netz39/PowerDelivery_for_Space/3D_models/PowerDelivery_Board.png

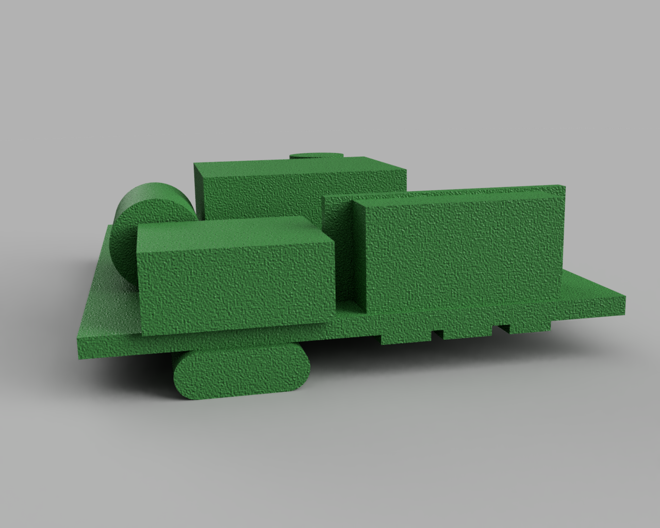
3D_models/PowerDelivery_Board.png
