netz39/PowerDelivery_for_Space/media/animatedView/frame.4.png

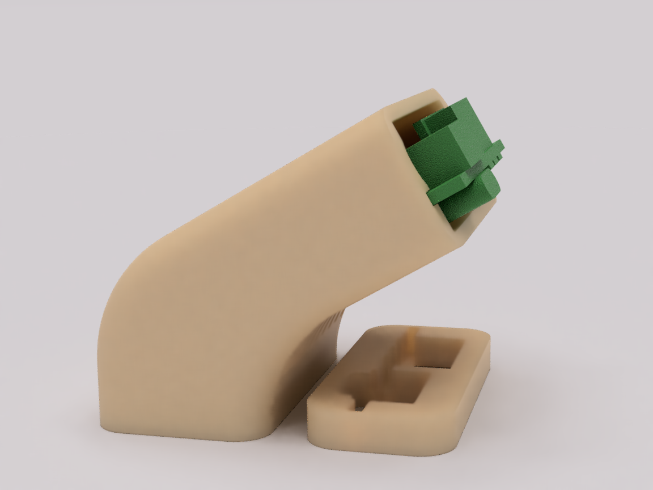
media/animatedView/frame.4.png
