netz39/PowerDelivery_for_Space/media/animatedView/frame.5.png

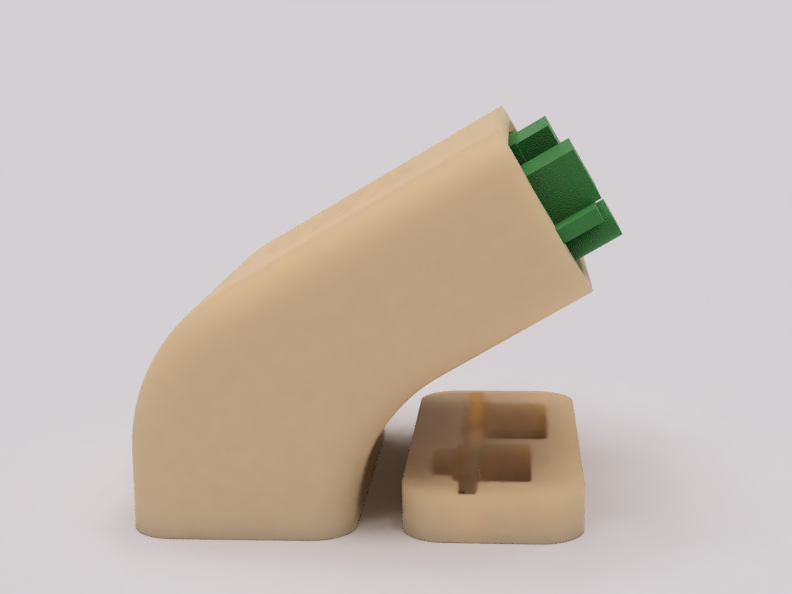
media/animatedView/frame.5.png
