netz39/PowerDelivery_for_Space/media/animatedView/frame.10.png

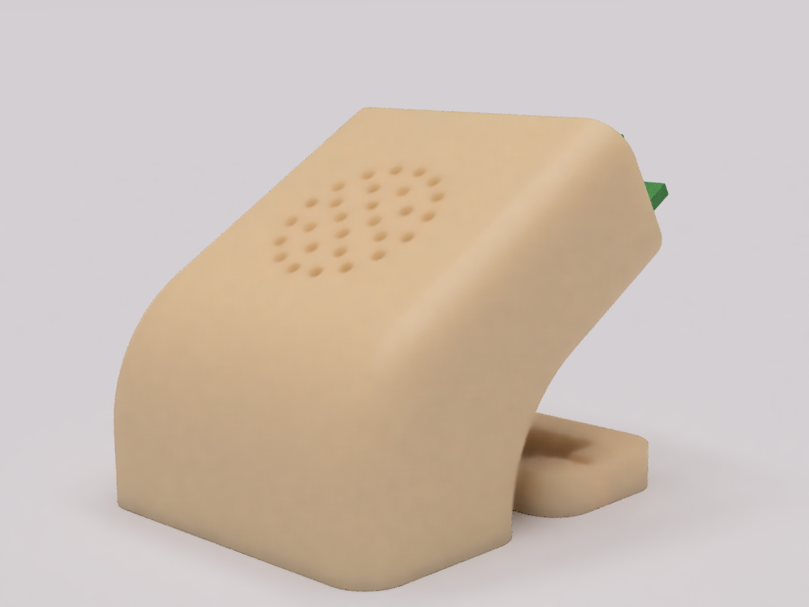
media/animatedView/frame.10.png
