netz39/PowerDelivery_for_Space/media/animatedView/frame.12.png

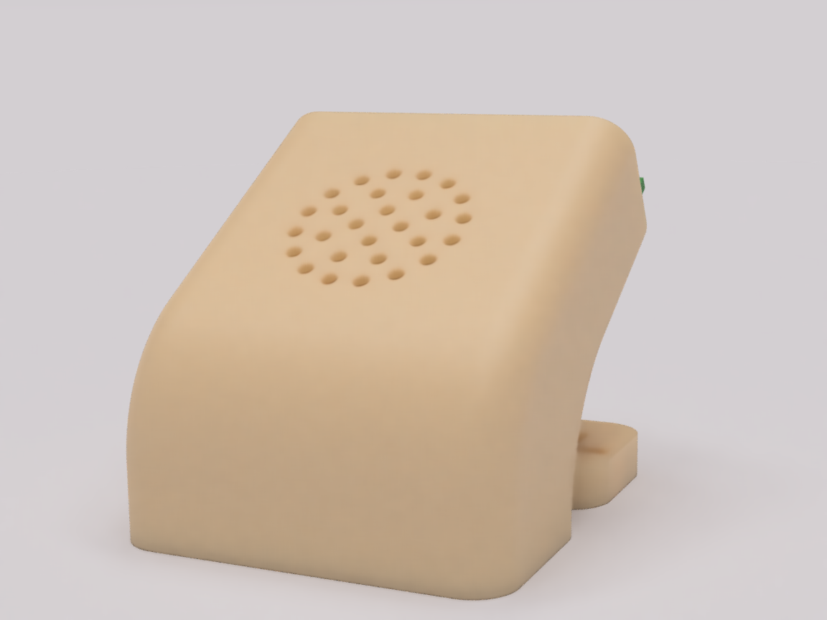
media/animatedView/frame.12.png
