netz39/PowerDelivery_for_Space/media/animatedView/frame.13.png

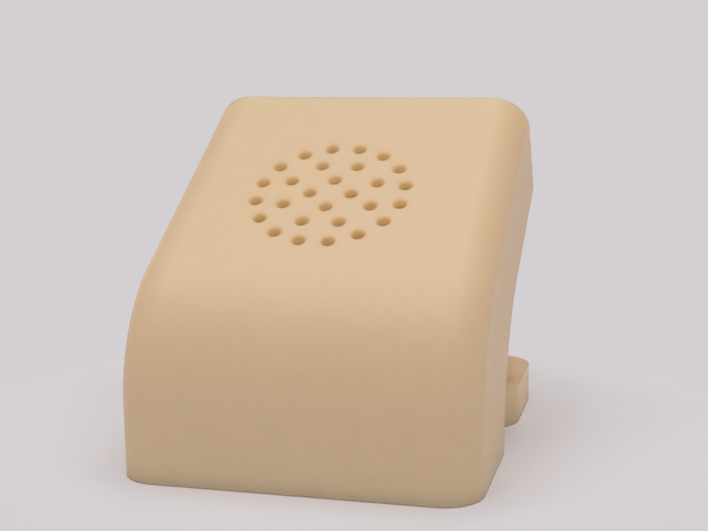
media/animatedView/frame.13.png
