netz39/PowerDelivery_for_Space/media/animatedView/frame.14.png

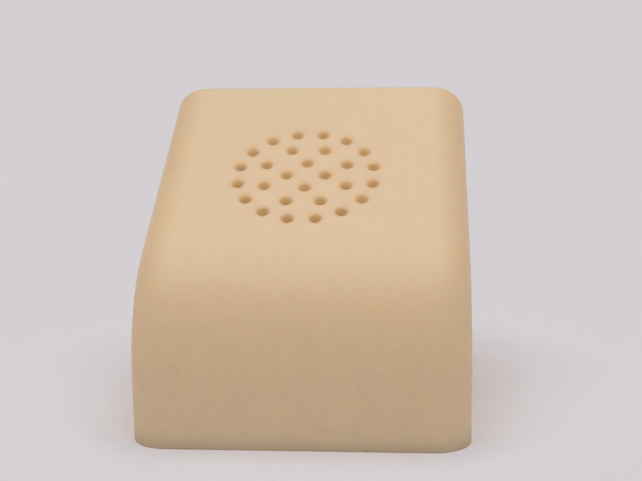
media/animatedView/frame.14.png
