netz39/PowerDelivery_for_Space/media/animatedView/frame.16.png

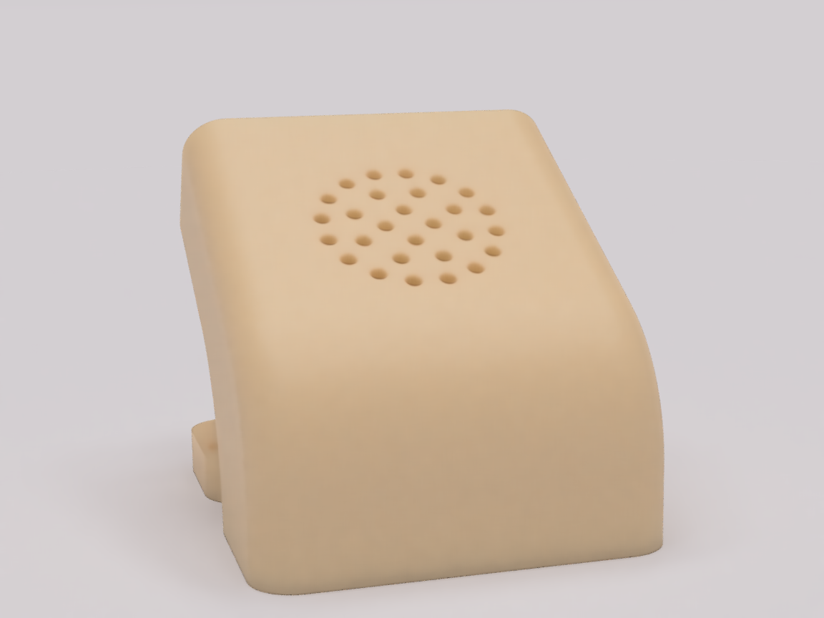
media/animatedView/frame.16.png
