netz39/PowerDelivery_for_Space/media/animatedView/frame.17.png

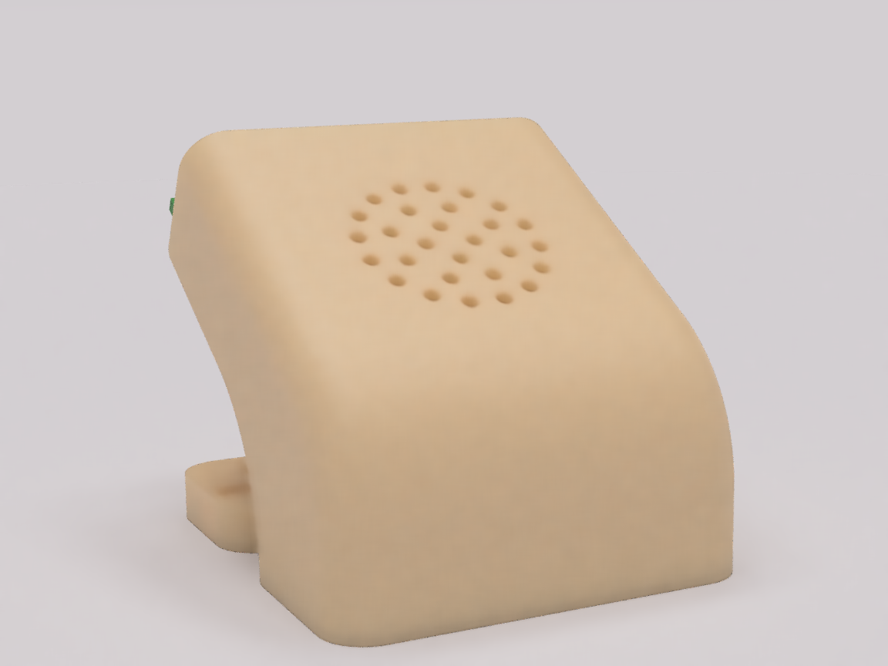
media/animatedView/frame.17.png
