netz39/PowerDelivery_for_Space/media/animatedView/frame.19.png

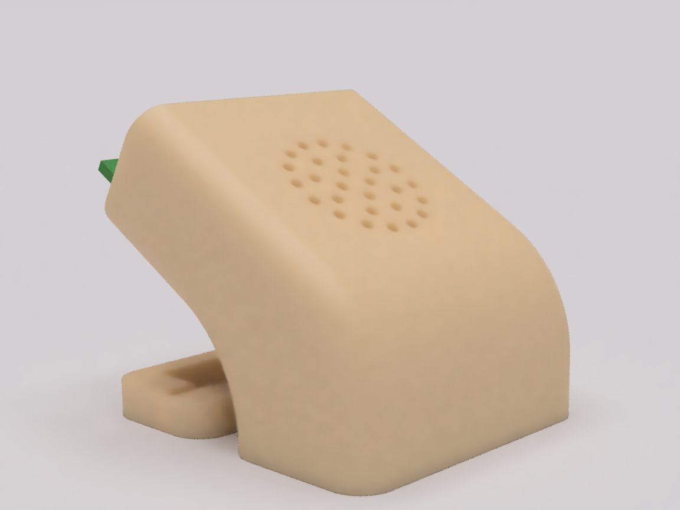
media/animatedView/frame.19.png
