netz39/PowerDelivery_for_Space/media/animatedView/frame.20.png

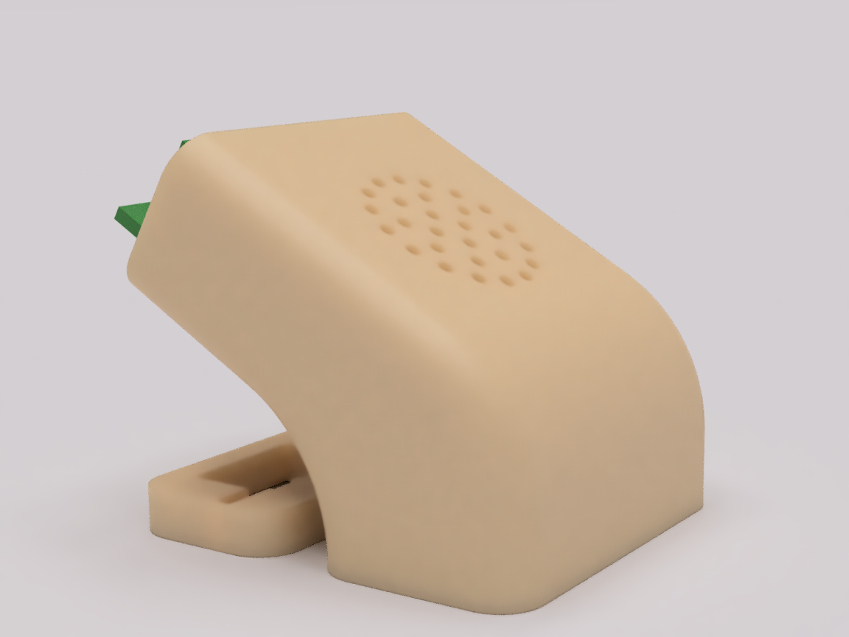
media/animatedView/frame.20.png
