netz39/PowerDelivery_for_Space/media/animatedView/frame.22.png

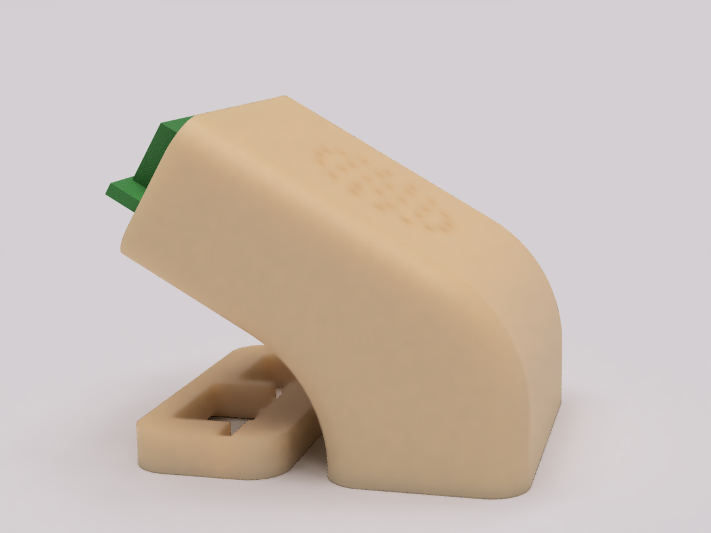
media/animatedView/frame.22.png
