netz39/PowerDelivery_for_Space/media/animatedView/frame.23.png

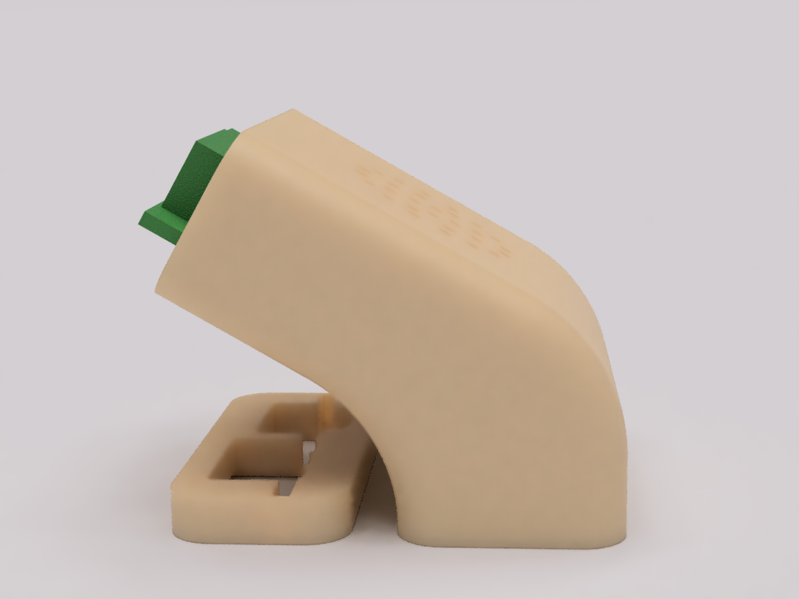
media/animatedView/frame.23.png
