netz39/PowerDelivery_for_Space/media/animatedView/frame.25.png

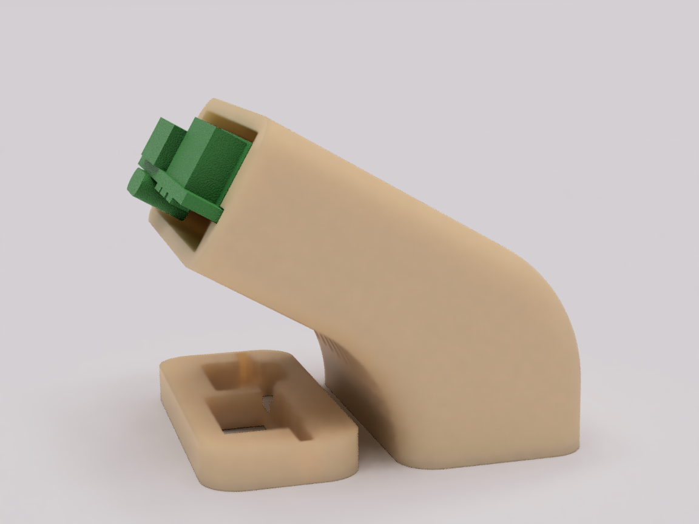
media/animatedView/frame.25.png
