netz39/PowerDelivery_for_Space/media/animatedView/frame.27.png

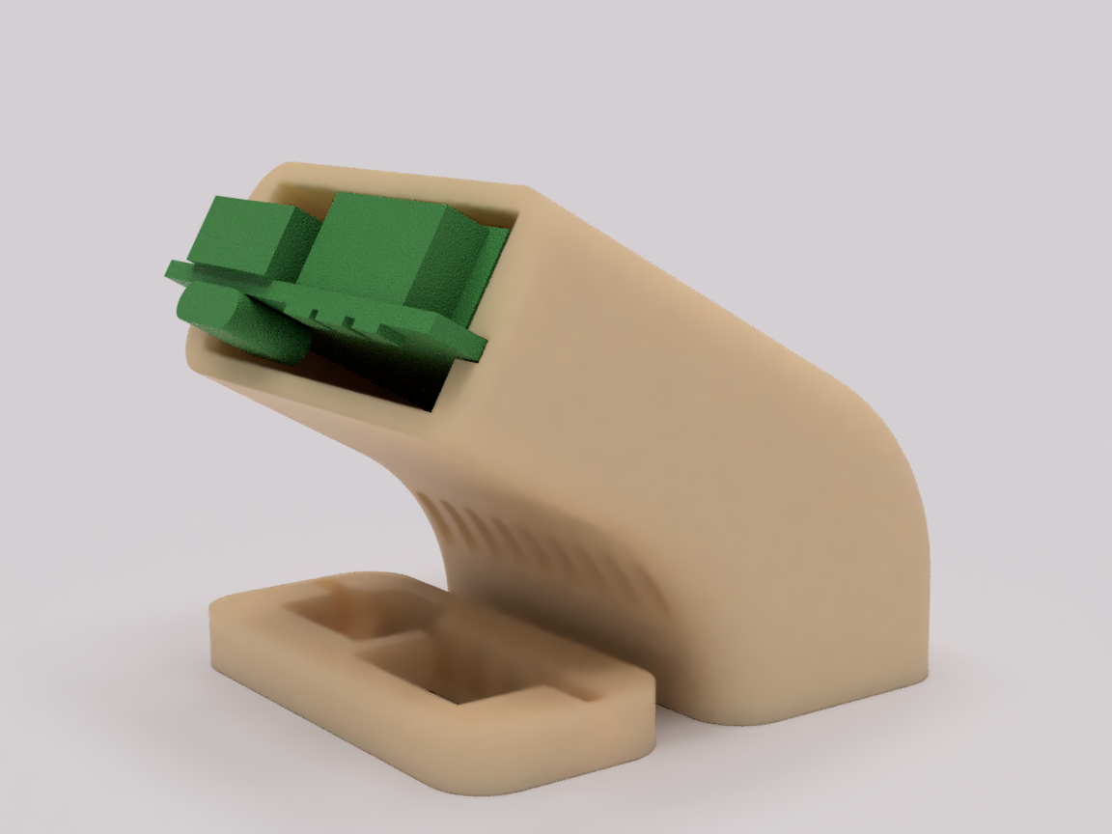
media/animatedView/frame.27.png
