netz39/PowerDelivery_for_Space/media/animatedView/frame.28.png

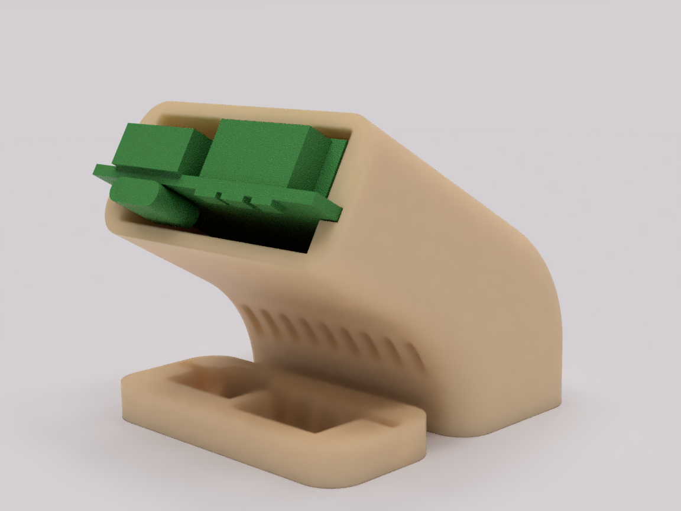
media/animatedView/frame.28.png
