netz39/PowerDelivery_for_Space/media/animatedView/frame.29.png

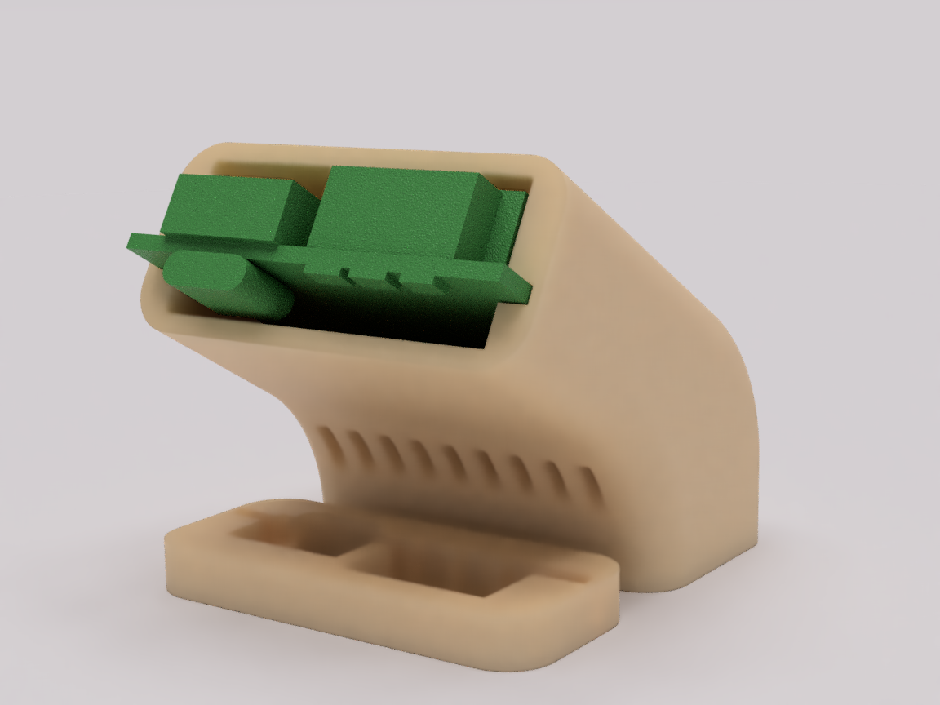
media/animatedView/frame.29.png
