netz39/PowerDelivery_for_Space/media/animatedView/frame.30.png

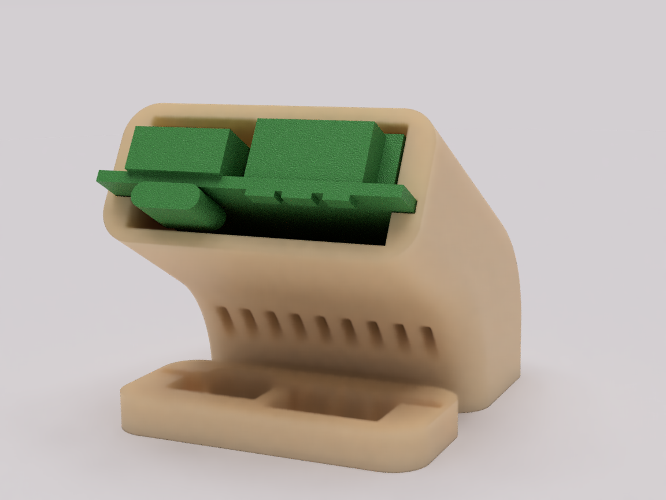
media/animatedView/frame.30.png
