netz39/PowerDelivery_for_Space/media/animatedView/frame.33.png

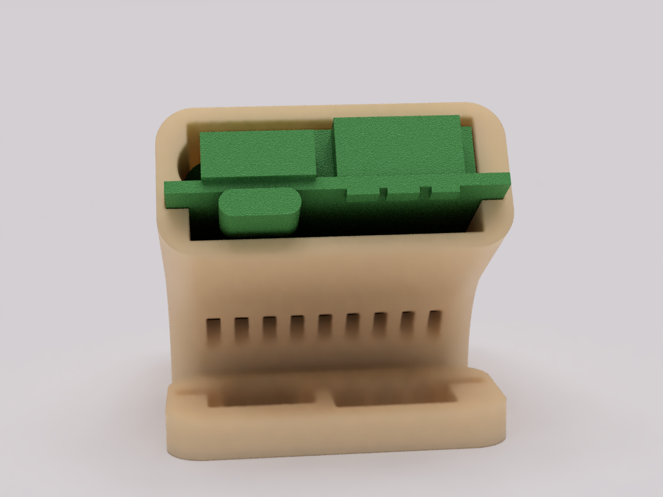
media/animatedView/frame.33.png
