netz39/PowerDelivery_for_Space/media/animatedView/frame.34.png

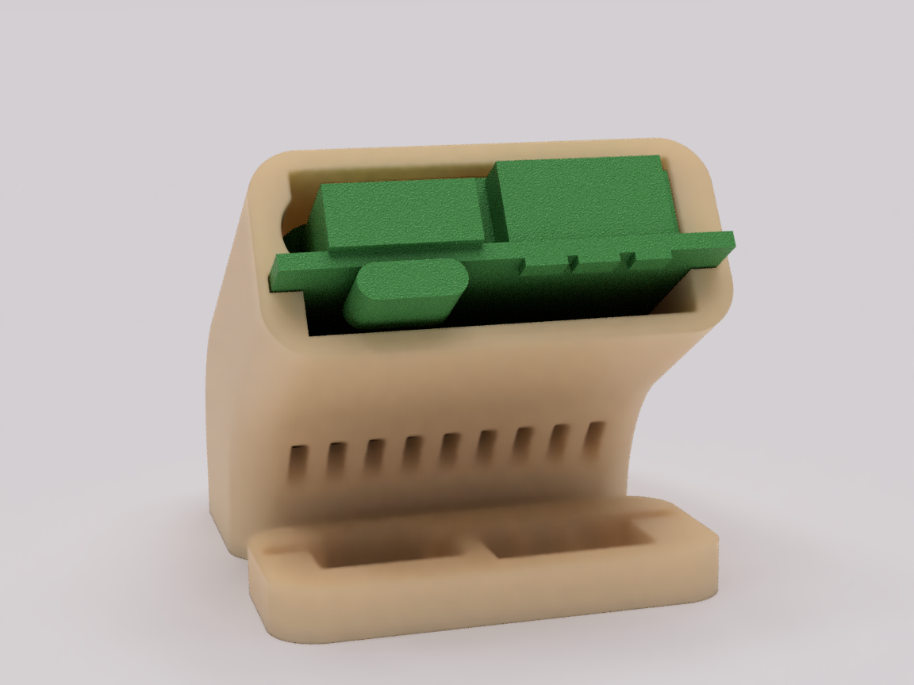
media/animatedView/frame.34.png
