netz39/PowerDelivery_for_Space/media/CAD_rendering_table2.png

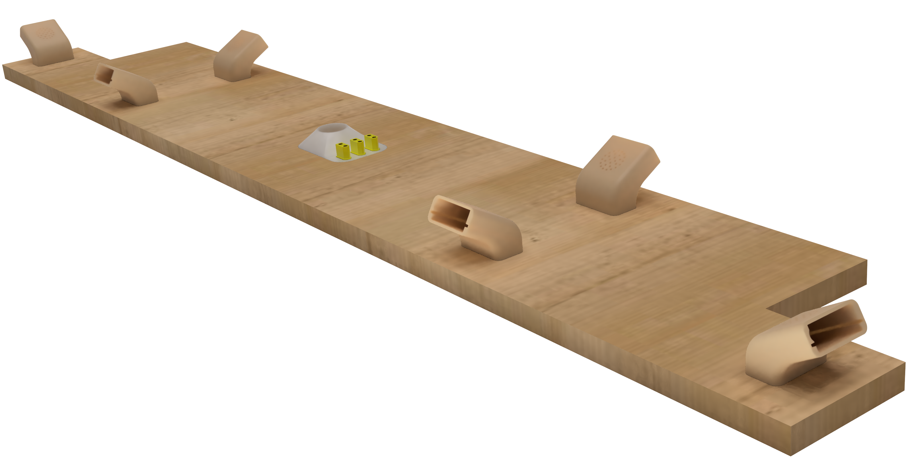
media/CAD_rendering_table2.png
