netz39/PowerDelivery_for_Space/media/PCB_Down.jpg

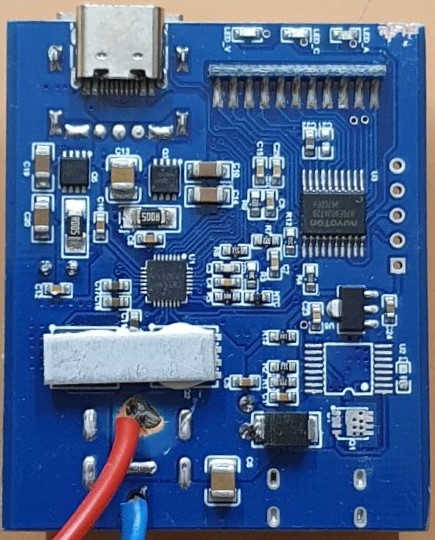
media/PCB_Down.jpg
