netz39/PowerDelivery_for_Space/media/PCB_Down_raw.jpg

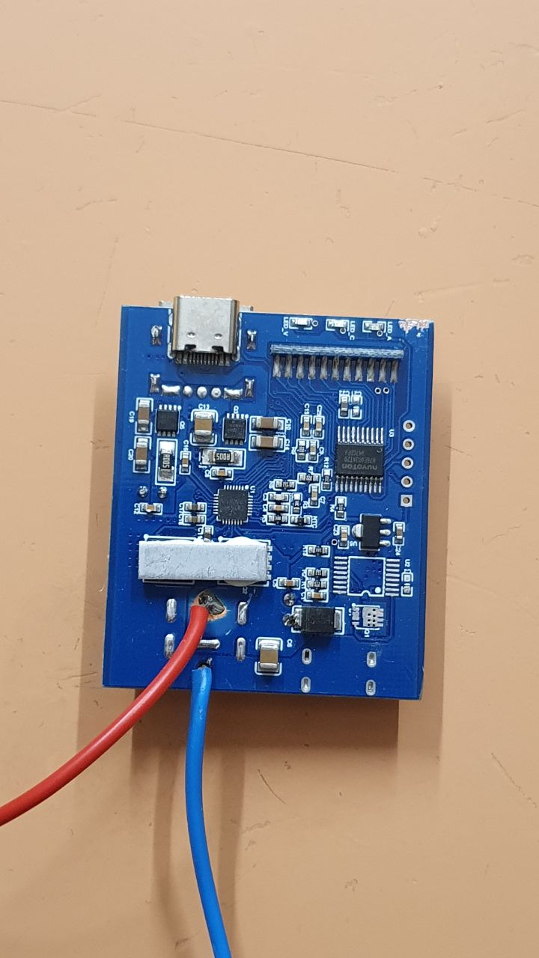
media/PCB_Down_raw.jpg
