netz39/PowerDelivery_for_Space/media/PCB_Top.jpg

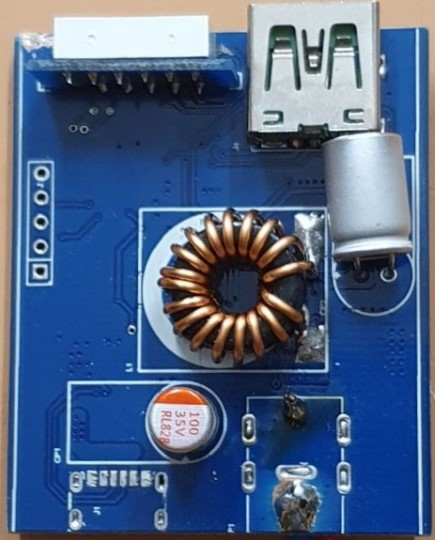
media/PCB_Top.jpg
