netz39/PowerDelivery_for_Space/media/PCB_Top_raw.jpg

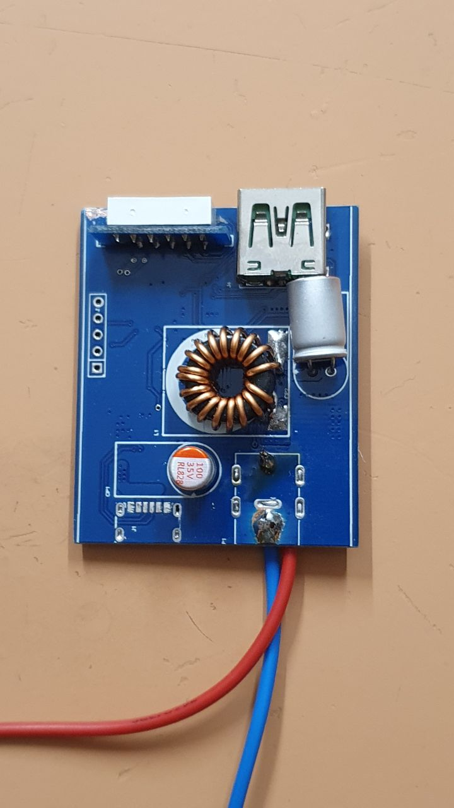
media/PCB_Top_raw.jpg
