netz39/PowerDelivery_for_Space/media/PDS100_3.jpg

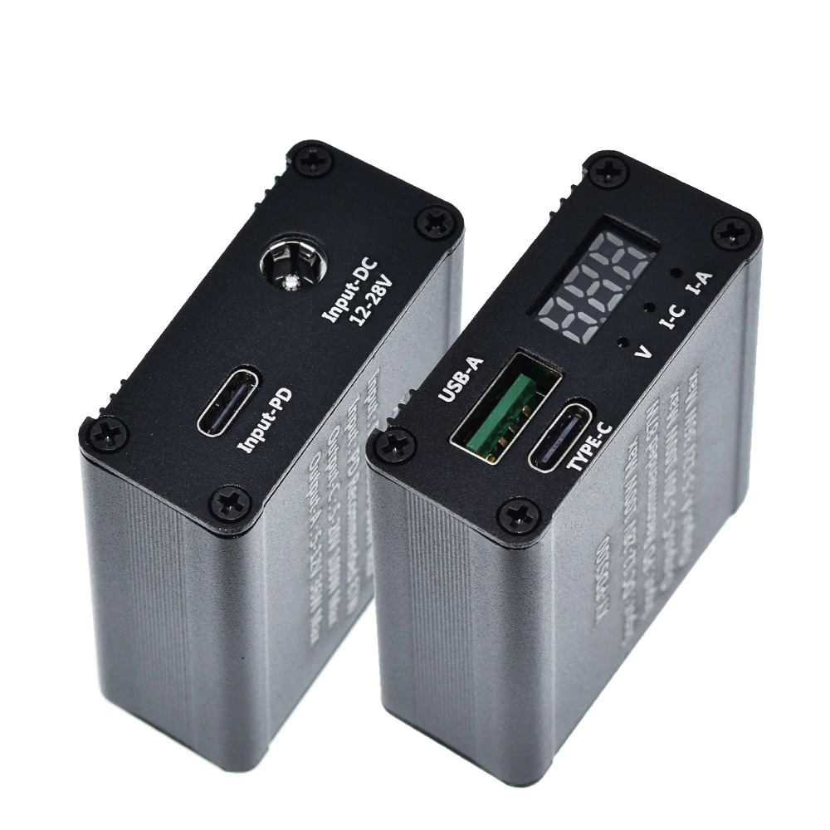
media/PDS100_3.jpg
