netz39/PowerDelivery_for_Space/media/ThermalCam_down2.JPG

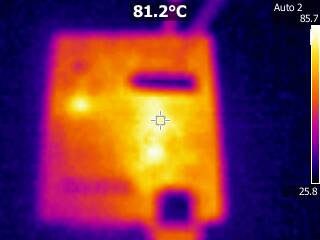
media/ThermalCam_down2.JPG
