netz39/PowerDelivery_for_Space/media/ThermalCam_top1.JPG

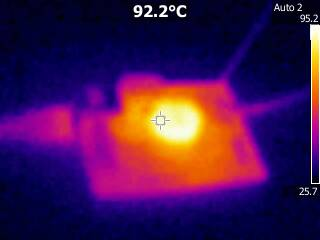
media/ThermalCam_top1.JPG
