netz39/PowerDelivery_for_Space/media/ThermalCam_top3.JPG

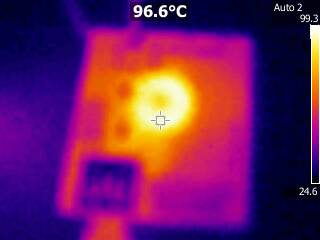
media/ThermalCam_top3.JPG
